alekseevpavel04/co2_detector/box/_sh_cut.png

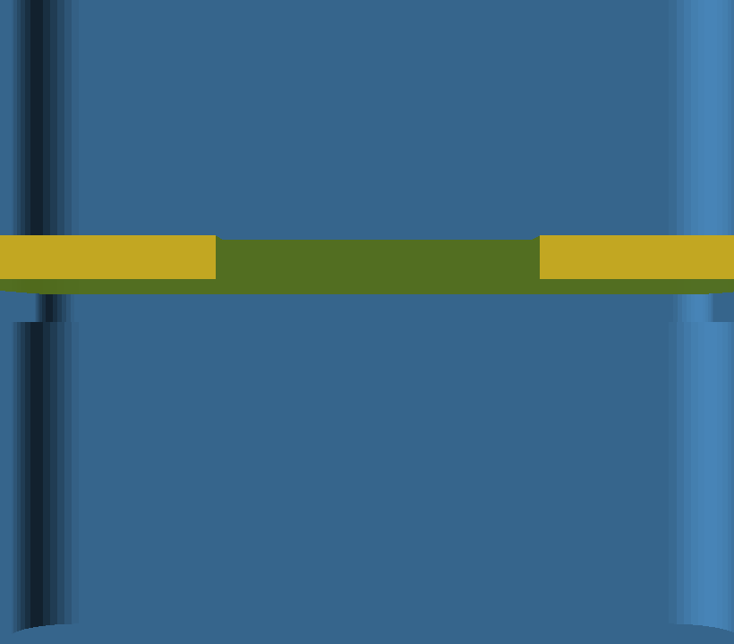
box/_sh_cut.png
