alekseevpavel04/co2_detector/box/_sh_zoom.png

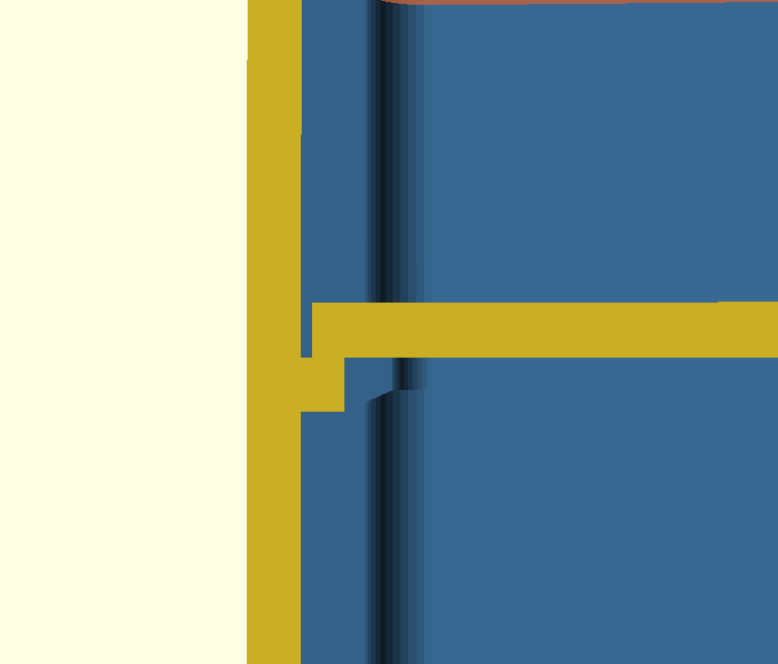
box/_sh_zoom.png
