alekseevpavel04/co2_detector/Дизайн экрана/fine.png

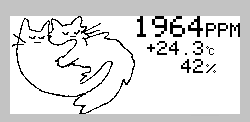
Дизайн экрана/fine.png
