alekseevpavel04/co2_detector/Дизайн экрана/График.png

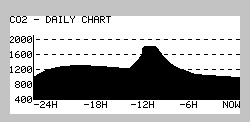
Дизайн экрана/График.png
