alekseevpavel04/co2_detector/Дизайн экрана/Шаблон2.png

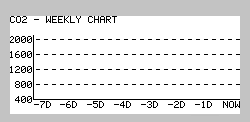
Дизайн экрана/Шаблон2.png
