alekseevpavel04/co2_detector/Дизайн экрана/Шаблон.png

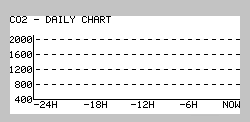
Дизайн экрана/Шаблон.png
