alekseevpavel04/co2_detector/src/mascot.h

// Авто-сгенерировано из норм.png (64x64, 1-bit FS-dither). Не редактировать руками.
#pragma once
#include <pgmspace.h>

#define MASCOT_W 64
#define MASCOT_H 64

const unsigned char MASCOT_GOOD[] PROGMEM = {
  0x00, 0x00, 0x00, 0x00, 0x00, 0x00, 0x00, 0x00, 0x00, 0x00, 0x00, 0x00,
  0x00, 0x00, 0x00, 0x00, 0x00, 0x00, 0x00, 0x00, 0x00, 0x00, 0x00, 0x00,
  0x00, 0x00, 0x00, 0x00, 0x00, 0x00, 0x00, 0x00, 0x00, 0x00, 0x00, 0x00,
  0x00, 0x00, 0x00, 0x00, 0x00, 0x00, 0x00, 0x00, 0x00, 0x00, 0x00, 0x00,
  0x00, 0x00, 0x00, 0x00, 0x00, 0x00, 0x00, 0x00, 0x00, 0x00, 0x00, 0x00,
  0x00, 0x00, 0x00, 0x00, 0x00, 0x00, 0x00, 0x00, 0x00, 0x00, 0x10, 0x00,
  0x00, 0x00, 0x00, 0x00, 0x00, 0x01, 0x00, 0x00, 0x00, 0x00, 0x80, 0x00,
  0x00, 0x08, 0x00, 0x00, 0x00, 0x00, 0x00, 0x04, 0x88, 0x00, 0x00, 0x00,
  0x00, 0x02, 0x01, 0x5B, 0x75, 0x00, 0x00, 0x00, 0x00, 0x00, 0x04, 0xEA,
  0xAC, 0xA4, 0x00, 0x00, 0x00, 0x00, 0x5D, 0x2D, 0xB2, 0x50, 0x00, 0x00,
  0x00, 0x00, 0x54, 0x56, 0xA9, 0x65, 0x00, 0x00, 0x00, 0x00, 0xDB, 0xDA,
  0xAE, 0xB1, 0x00, 0x00, 0x00, 0x03, 0x0D, 0x56, 0xA8, 0xC4, 0xE0, 0x00,
  0x00, 0x02, 0x4A, 0xBA, 0xAC, 0x50, 0x10, 0x00, 0x00, 0x09, 0x01, 0x95,
  0x52, 0x3F, 0x08, 0x00, 0x00, 0x17, 0xFA, 0xD5, 0x50, 0xFF, 0xE8, 0x00,
  0x00, 0x4F, 0x75, 0x52, 0x55, 0xE9, 0xF6, 0x00, 0x00, 0x1D, 0xD9, 0xAA,
  0xC3, 0xFD, 0xF5, 0x00, 0x01, 0xF7, 0xB4, 0xAA, 0x57, 0xA2, 0xAE, 0x00,
  0x01, 0x2E, 0xFF, 0x52, 0xA7, 0xFA, 0xD1, 0x80, 0x06, 0x9F, 0xAE, 0xA5,
  0xAA, 0x83, 0x3B, 0x80, 0x03, 0xA5, 0xFD, 0x12, 0x6F, 0x1E, 0xCE, 0xC0,
  0x04, 0xE7, 0x65, 0x6A, 0xCA, 0xF7, 0xDB, 0x68, 0x07, 0xF4, 0x8A, 0xBF,
  0x75, 0xB9, 0x6E, 0x30, 0x05, 0x5F, 0x76, 0xCA, 0xCA, 0xDE, 0xB3, 0xD0,
  0x0F, 0xF5, 0xBA, 0xD5, 0x75, 0xB0, 0x57, 0x28, 0x0B, 0x5E, 0xD5, 0x75,
  0xE2, 0xEA, 0x94, 0xA8, 0x06, 0xFB, 0xAC, 0xFA, 0xD3, 0x4A, 0xD5, 0x44,
  0x0D, 0xDD, 0xF5, 0x17, 0xEA, 0x90, 0x05, 0x28, 0x07, 0x77, 0x54, 0x5B,
  0x84, 0x5D, 0xDA, 0xE6, 0x1B, 0x5D, 0xD1, 0x0D, 0x53, 0xB6, 0x6D, 0xB4,
  0x05, 0xE8, 0x64, 0xA7, 0x94, 0xE3, 0xAA, 0xD8, 0x35, 0x75, 0xAA, 0xA1,
  0x0A, 0x0A, 0x16, 0xB4, 0x2F, 0xD5, 0x90, 0x91, 0x54, 0xA4, 0xD4, 0x54,
  0x34, 0x54, 0x64, 0x85, 0x8A, 0x02, 0x5B, 0x56, 0x5F, 0x8F, 0x9A, 0xA9,
  0xE1, 0x59, 0x45, 0x50, 0x70, 0xE9, 0xA2, 0x0B, 0xFC, 0x76, 0xB5, 0x3B,
  0x9F, 0x2A, 0x49, 0x57, 0xF3, 0xF5, 0x56, 0x80, 0x6A, 0xA2, 0xA4, 0xAF,
  0xD7, 0xFA, 0x99, 0x5A, 0xDA, 0x96, 0x53, 0x35, 0xD7, 0xD5, 0x46, 0x2D,
  0x6A, 0x4B, 0x8A, 0xEA, 0xD7, 0x24, 0x39, 0x84, 0xD9, 0x56, 0xAC, 0xF5,
  0x5E, 0x11, 0x4A, 0x7B, 0x75, 0x96, 0xEB, 0xFA, 0x55, 0x55, 0x2B, 0xAC,
  0x9A, 0x6B, 0x56, 0xFD, 0x2D, 0x41, 0x4D, 0xAA, 0x7E, 0xF4, 0xBB, 0xDB,
  0xEA, 0x15, 0x7E, 0xD4, 0x53, 0x5A, 0xAA, 0x77, 0x55, 0x41, 0x53, 0x2A,
  0x17, 0xAE, 0xAD, 0x9D, 0x48, 0x93, 0x74, 0xA8, 0x1C, 0xD4, 0xB6, 0xD5,
  0x44, 0x88, 0x8A, 0xA5, 0x16, 0xAA, 0x4A, 0x55, 0x2A, 0x22, 0x6A, 0x94,
  0x12, 0xAA, 0xB5, 0xAA, 0x81, 0x59, 0x2A, 0x68, 0x0A, 0xA9, 0x56, 0xB4,
  0x9A, 0x24, 0xA5, 0x52, 0x05, 0x54, 0x9A, 0xAA, 0xA5, 0x4A, 0x55, 0x55,
  0x02, 0x8A, 0x52, 0x55, 0x48, 0xA1, 0x2A, 0xA8, 0x0D, 0x51, 0x55, 0x4A,
  0x95, 0x2A, 0x95, 0x25, 0x02, 0x95, 0x5A, 0xB5, 0x44, 0x94, 0xA5, 0x11,
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
};

// Пока все стадии — одна картинка (позже заменим на 3 состояния)
#define MASCOT_FAIR MASCOT_GOOD
#define MASCOT_POOR MASCOT_GOOD
